bhuvan21/SenseBorg/build/images/schematic.jpg

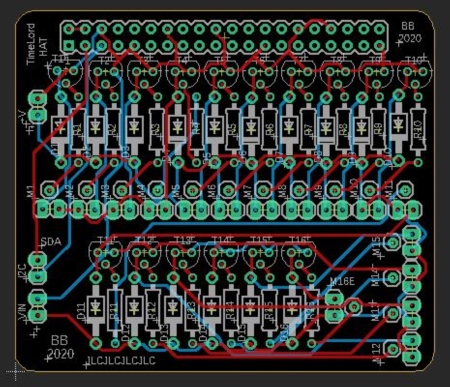
build/images/schematic.jpg
